Infinity-Stumps/infinity-stumps/simulation/outputs/sim03_trajectory_recovery.png

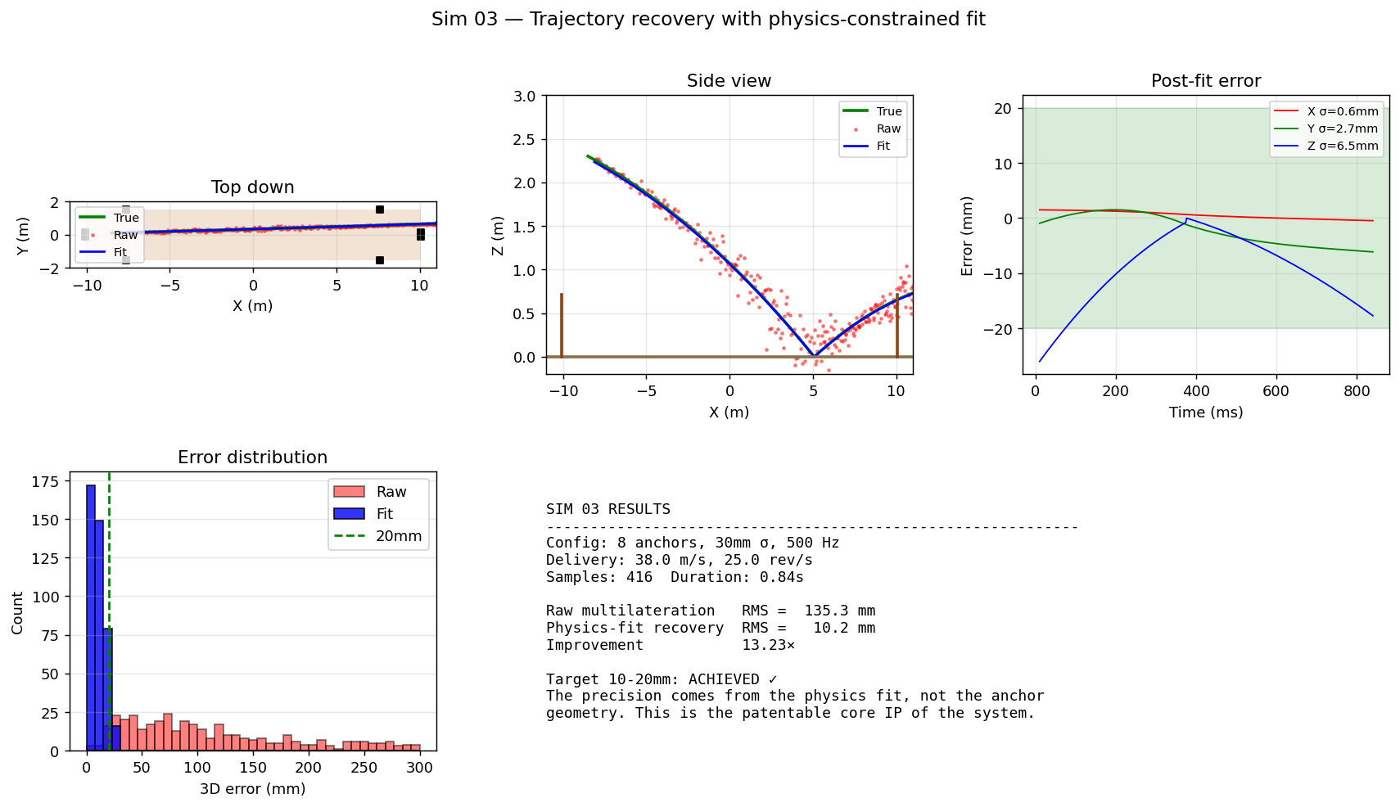
simulation/outputs/sim03_trajectory_recovery.png
