Infinity-Stumps/infinity-stumps/simulation/outputs/sim05_multipath_occlusion.png

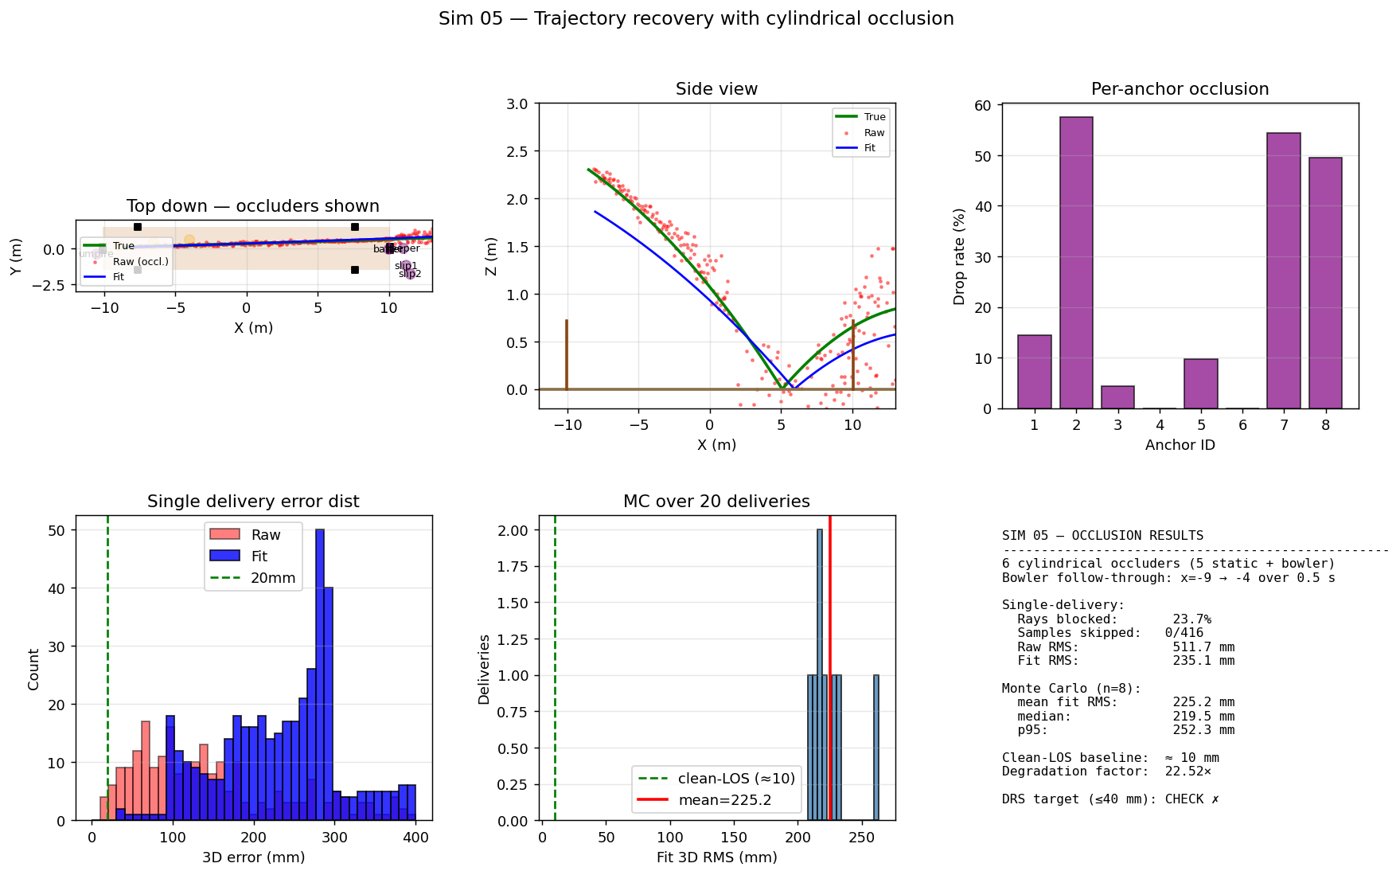
simulation/outputs/sim05_multipath_occlusion.png
