Infinity-Stumps/infinity-stumps/simulation/outputs/sim05b_mitigations.png

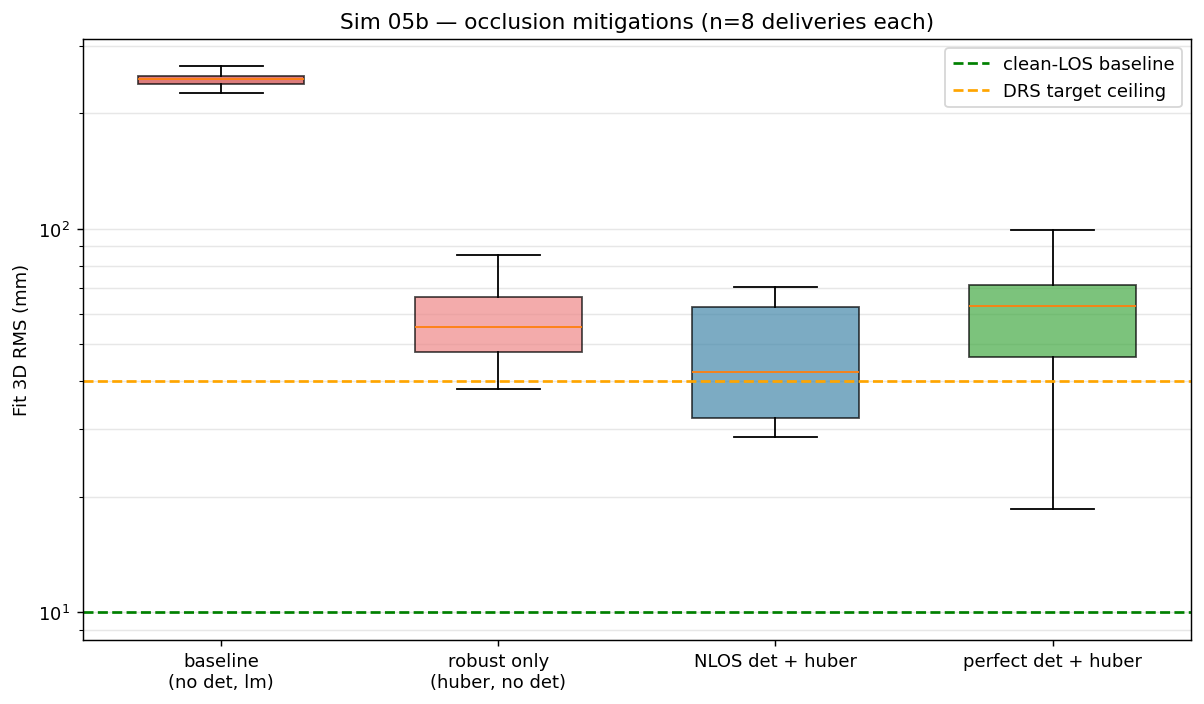
simulation/outputs/sim05b_mitigations.png
