Infinity-Stumps/infinity-stumps/simulation/outputs/sim_ekf.png

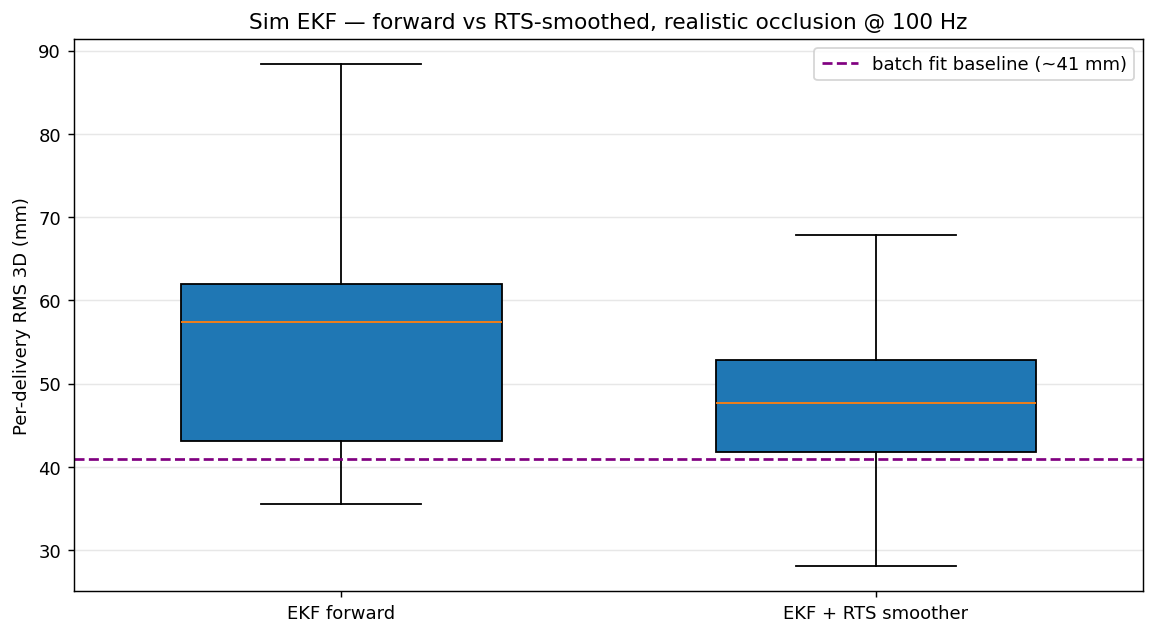
simulation/outputs/sim_ekf.png
