Infinity-Stumps/infinity-stumps/simulation/outputs/sim_lbw.png

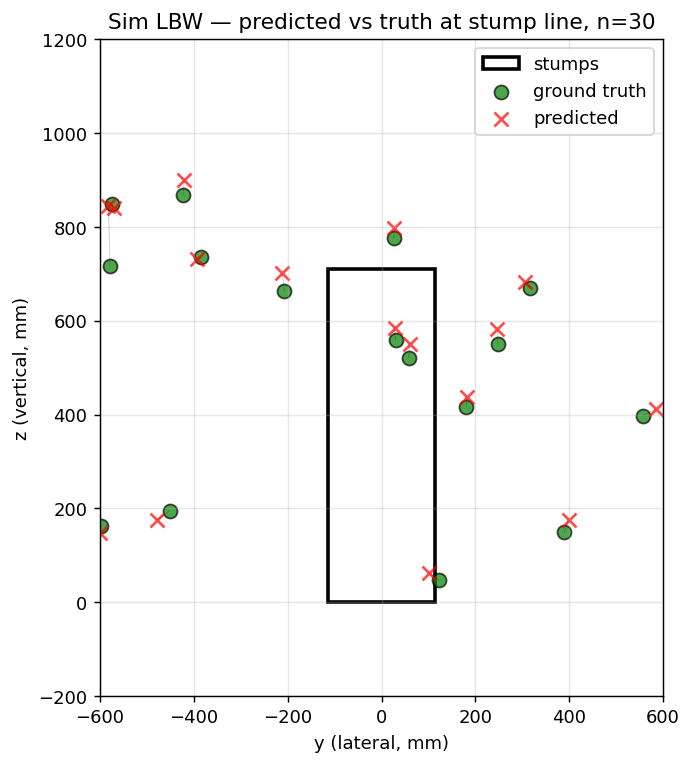
simulation/outputs/sim_lbw.png
