Infinity-Stumps/infinity-stumps/simulation/outputs/sim_ml.png

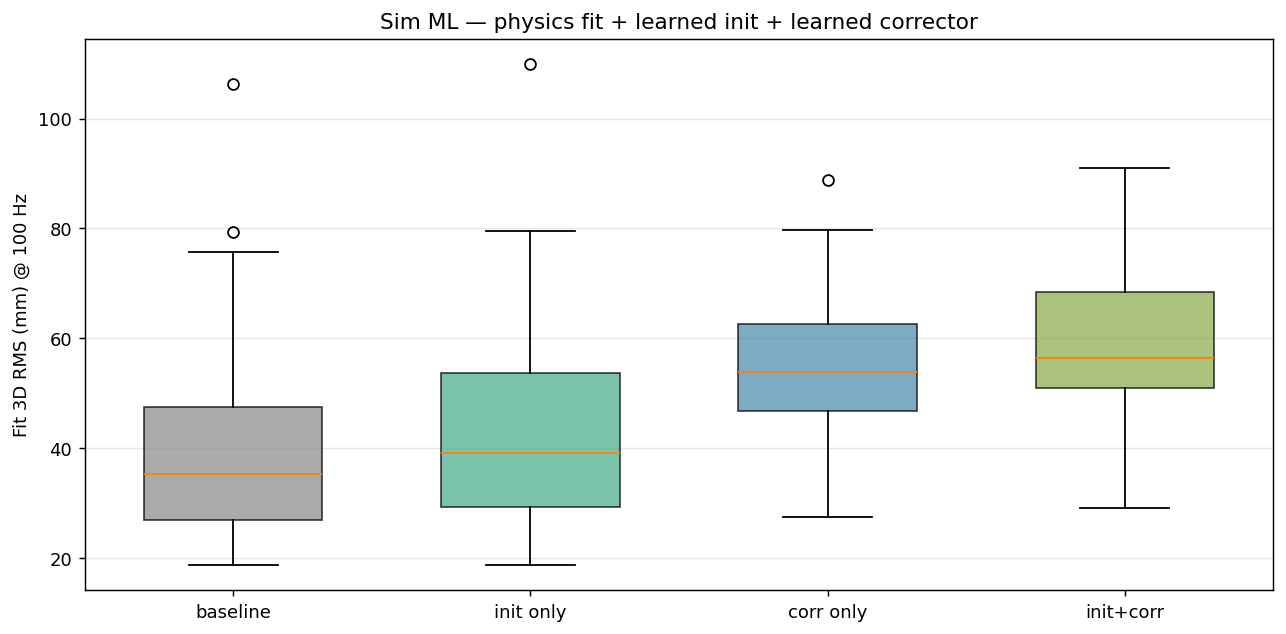
simulation/outputs/sim_ml.png
