Infinity-Stumps/infinity-stumps/simulation/outputs/sim_realistic.png

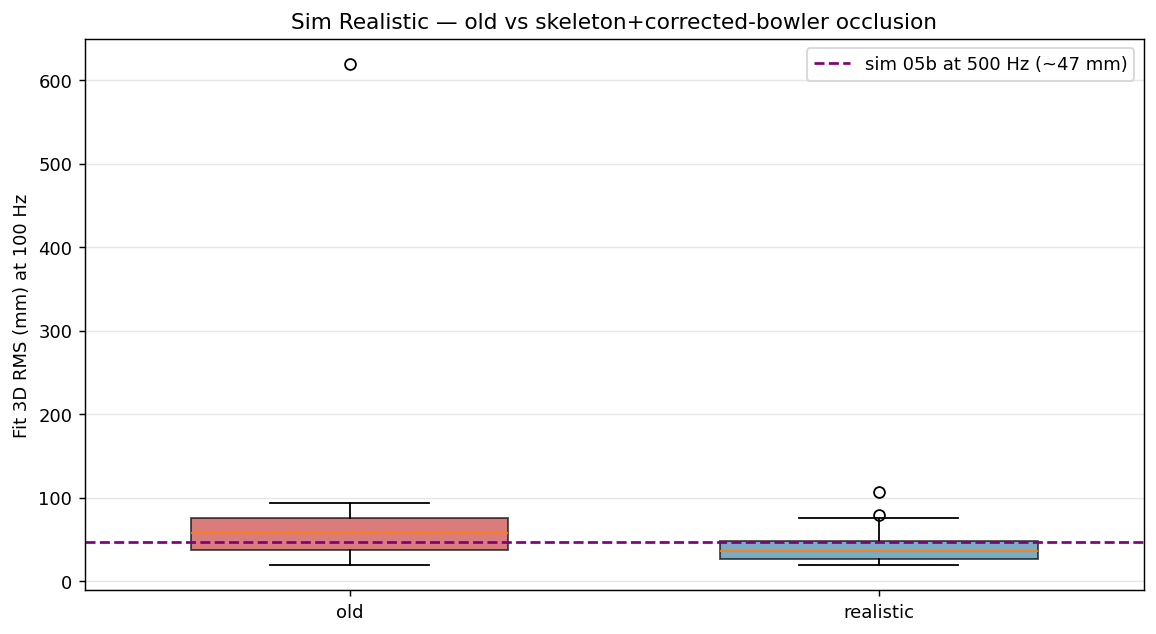
simulation/outputs/sim_realistic.png
