Infinity-Stumps/infinity-stumps/simulation/outputs/upside_sweep.png

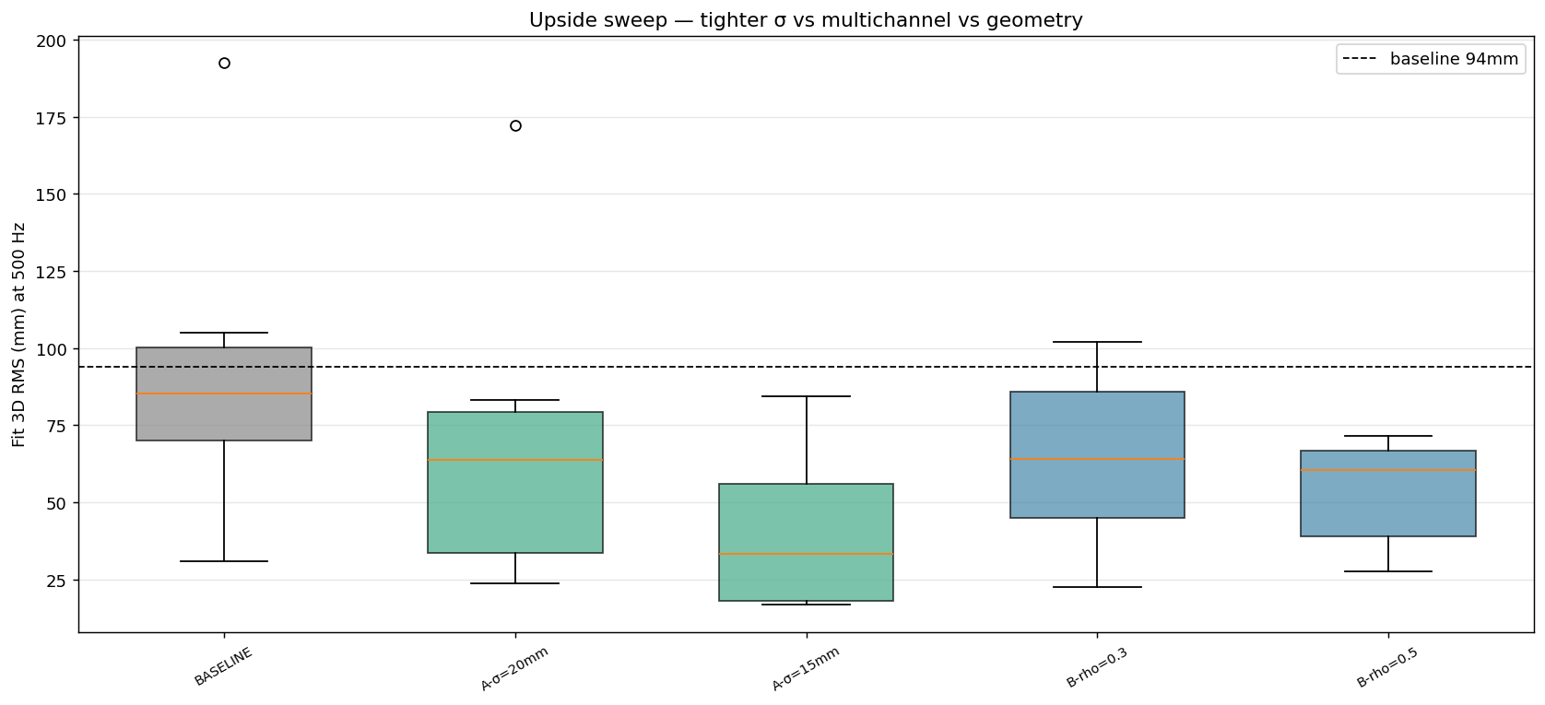
simulation/outputs/upside_sweep.png
