Infinity-Stumps/infinity-stumps/hardware/anchor-board/anchor_board.kicad_sch

## KiCad design hardware/anchor-board/anchor_board.kicad_sch (2026-05-14)

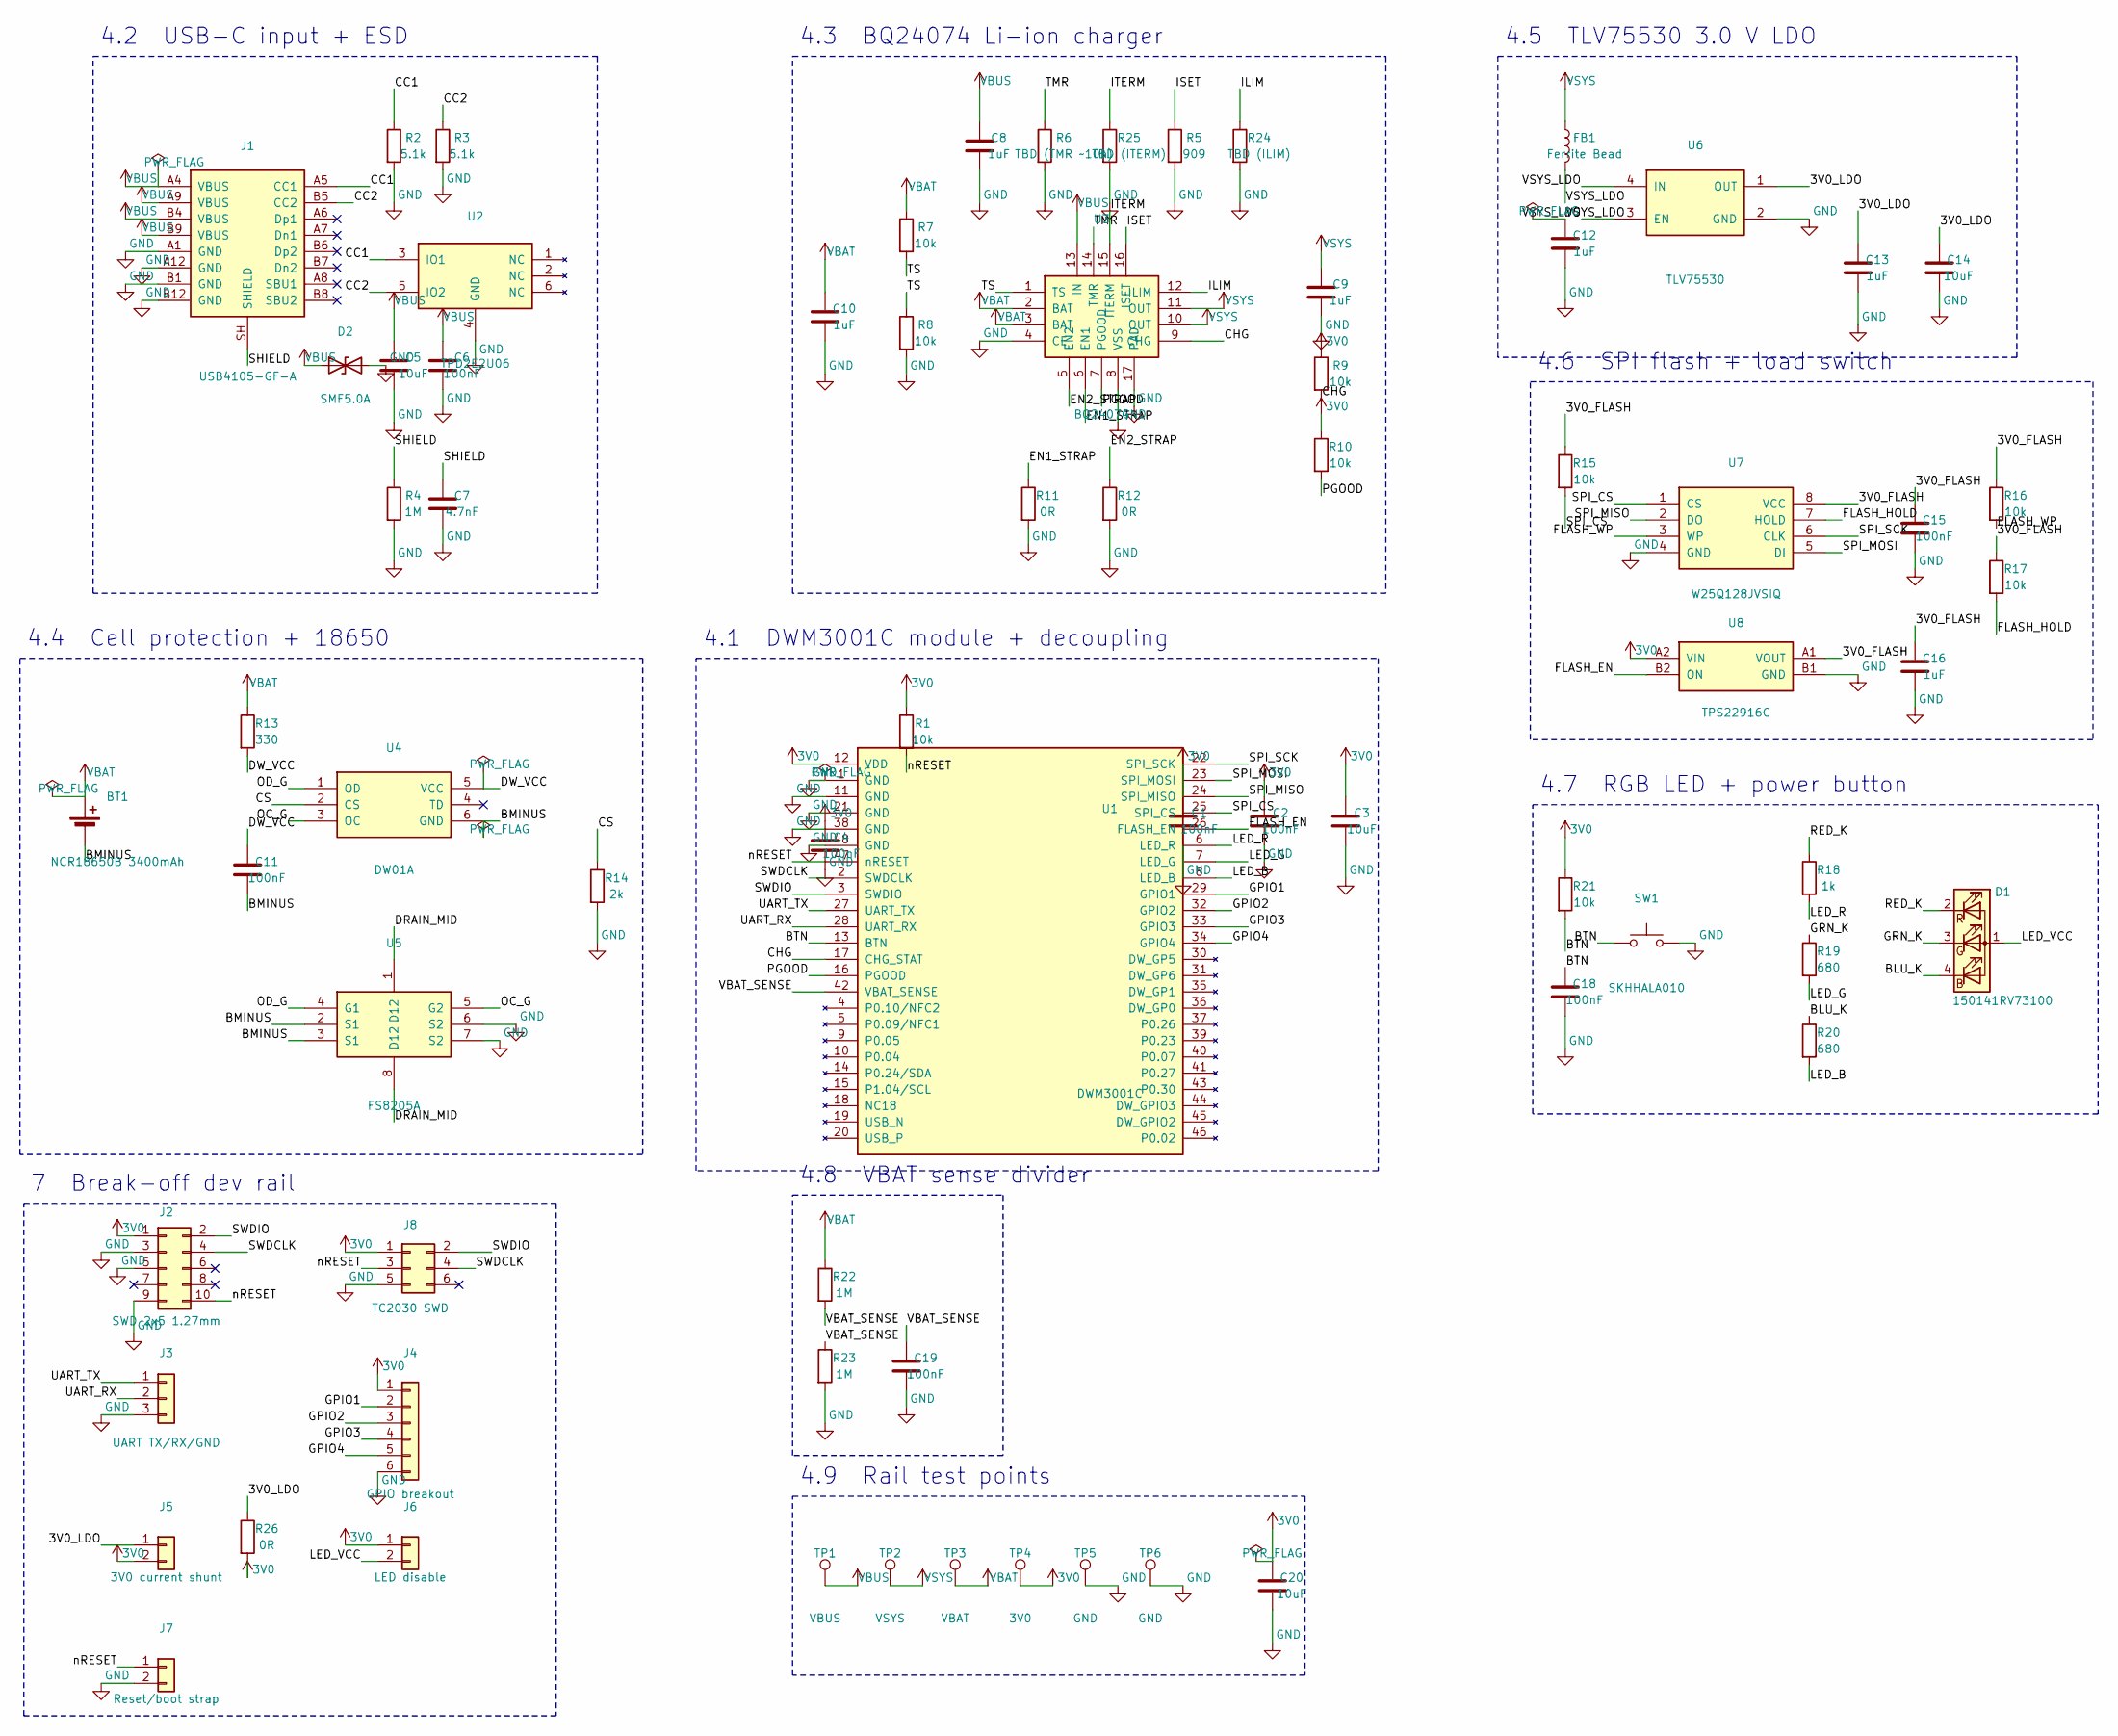
[picture p10: schematic anchor_board.kicad_sch]

Parts:
BT1: NCR18650B 3400mAh; BatteryHolder_Keystone_1042_1x18650
C1, C2, C4, C6, C11, C15, C18, C19: 100nF; C_0402_1005Metric
C3, C5, C14, C20: 10uF; C_0805_2012Metric
C7: 4.7nF; C_0402_1005Metric
C8, C9, C10, C12, C13, C16: 1uF; C_0603_1608Metric
D1: 150141RV73100; LED_RGB_Wuerth-PLCC4_3.2x2.8mm_150141M173100
D2: SMF5.0A; D_SOD-123
FB1: Ferrite Bead; L_0603_1608Metric
J1: USB4105-GF-A; USB_C_Receptacle_GCT_USB4105-xx-A_16P_TopMnt_Horizontal
J2: SWD 2x5 1.27mm; PinHeader_2x05_P1.27mm_Vertical
J3: UART TX/RX/GND; PinHeader_1x03_P2.54mm_Vertical
J4: GPIO breakout; PinHeader_1x06_P2.54mm_Vertical
J5: 3V0 current shunt; PinHeader_1x02_P2.54mm_Vertical
J6: LED disable; PinHeader_1x02_P2.54mm_Vertical
J7: Reset/boot strap; PinHeader_1x02_P2.54mm_Vertical
J8: TC2030 SWD; Tag-Connect_TC2030-IDC-NL_2x03_P1.27mm_Vertical
R1, R7, R8, R9, R10, R15, R16, R17, R21: 10k; R_0402_1005Metric
R2, R3: 5.1k; R_0402_1005Metric
R4, R22, R23: 1M; R_0402_1005Metric
R5: 909; R_0402_1005Metric
R6: TBD (TMR ~10h); R_0402_1005Metric
R11, R12, R26: 0R; R_0402_1005Metric
R13: 330; R_0402_1005Metric
R14: 2k; R_0402_1005Metric
R18: 1k; R_0402_1005Metric
R19, R20: 680; R_0402_1005Metric
R24: TBD (ILIM); R_0402_1005Metric
R25: TBD (ITERM); R_0402_1005Metric
SW1: SKHHALA010; SW_Alps_SKHHAL
TP1: VBUS; TestPoint_Pad_D1.5mm
TP2: VSYS; TestPoint_Pad_D1.5mm
TP3: VBAT; TestPoint_Pad_D1.5mm
TP4: 3V0; TestPoint_Pad_D1.5mm
TP5, TP6: GND; TestPoint_Pad_D1.5mm
U1: DWM3001C
U2: TPD2E2U06; SOT-563
U3: BQ24074; QFN-16-1EP_3x3mm_P0.5mm_EP1.7x1.7mm
U4: DW01A; SOT-23-6
U5: FS8205A; TSSOP-8_4.4x3mm_P0.65mm
U6: TLV75530; X2SON-4_1x1mm_P0.5mm
U7: W25Q128JVSIQ; SOIC-8_3.9x4.9mm_P1.27mm
U8: TPS22916C; WLP-4_0.83x0.83mm_P0.4mm

Connections:
3V0: C1.1, C2.1, C3.1, C4.1, C20.1, J2.1, J4.1, J5.2, J6.1, J8.1, R1.1, R9.1, R10.1, R21.1, R26.2, TP4.1, U1.12 (VDD), U8.A2 (VIN)
3V0_FLASH: C15.1, C16.1, R15.1, R16.1, R17.1, U7.8 (VCC), U8.A1 (VOUT)
3V0_LDO: C13.1, C14.1, J5.1, R26.1, U6.1 (OUT)
BLU_K: D1.4 (BK), R20.1
BMINUS: BT1.2 (-), C11.2, U4.6 (GND), U5.2 (S1), U5.3 (S1)
BTN: C18.1, R21.2, SW1.1, U1.13 (BTN)
CC1: J1.A5 (CC1), R2.1, U2.3 (IO1)
CC2: J1.B5 (CC2), R3.1, U2.5 (IO2)
CHG: R9.2, U1.17 (CHG_STAT), U3.9 (CHG)
CS: R14.1, U4.2 (CS)
DRAIN_MID: U5.1 (D12), U5.8 (D12)
DW_VCC: C11.1, R13.2, U4.5 (VCC)
EN1_STRAP: R11.1, U3.6 (EN1)
EN2_STRAP: R12.1, U3.5 (EN2)
FLASH_EN: U1.26 (FLASH_EN), U8.B2 (ON)
FLASH_HOLD: R17.2, U7.7 (HOLD)
FLASH_WP: R16.2, U7.3 (WP)
GND: C1.2, C2.2, C3.2, C4.2, C5.2, C6.2, C7.2, C8.2, C9.2, C10.2, C12.2, C13.2, C14.2, C15.2, C16.2, C18.2, C19.2, C20.2, D2.2 (A2), J1.A1 (GND), J1.A12 (GND), J1.B1 (GND), J1.B12 (GND), J2.3, J2.5, J2.9, J3.3, J4.6, J7.2, J8.5, R2.2, R3.2, R4.2, R5.2, R6.2, R8.2, R11.2, R12.2, R14.2, R23.2, R24.2, R25.2, SW1.2, TP5.1, TP6.1, U1.1 (GND), U1.11 (GND), U1.21 (GND), U1.38 (GND), U1.48 (GND), U2.4 (GND), U3.4 (CE), U3.8 (VSS), U3.17 (PAD), U5.6 (S2), U5.7 (S2), U6.2 (GND), U7.4 (GND), U8.B1 (GND)
GPIO1: J4.2, U1.29 (GPIO1)
GPIO2: J4.3, U1.32 (GPIO2)
GPIO3: J4.4, U1.33 (GPIO3)
GPIO4: J4.5, U1.34 (GPIO4)
GRN_K: D1.3 (GK), R19.1
ILIM: R24.1, U3.12 (ILIM)
ISET: R5.1, U3.16 (ISET)
ITERM: R25.1, U3.15 (ITERM)
LED_B: R20.2, U1.8 (LED_B)
LED_G: R19.2, U1.7 (LED_G)
LED_R: R18.2, U1.6 (LED_R)
LED_VCC: D1.1 (A), J6.2
OC_G: U4.3 (OC), U5.5 (G2)
OD_G: U4.1 (OD), U5.4 (G1)
PGOOD: R10.2, U1.16 (PGOOD), U3.7 (PGOOD)
RED_K: D1.2 (RK), R18.1
SHIELD: C7.1, J1.SH (SHIELD), R4.1
SPI_CS: R15.2, U1.25 (SPI_CS), U7.1 (CS)
SPI_MISO: U1.24 (SPI_MISO), U7.2 (DO)
SPI_MOSI: U1.23 (SPI_MOSI), U7.5 (DI)
SPI_SCK: U1.22 (SPI_SCK), U7.6 (CLK)
SWDCLK: J2.4, J8.4, U1.2 (SWDCLK)
SWDIO: J2.2, J8.2, U1.3 (SWDIO)
TMR: R6.1, U3.14 (TMR)
TS: R7.2, R8.1, U3.1 (TS)
UART_RX: J3.2, U1.28 (UART_RX)
UART_TX: J3.1, U1.27 (UART_TX)
VBAT: BT1.1 (+), C10.1, R7.1, R13.1, R22.1, TP3.1, U3.2 (BAT), U3.3 (BAT)
VBAT_SENSE: C19.1, R22.2, R23.1, U1.42 (VBAT_SENSE)
VBUS: C5.1, C6.1, C8.1, D2.1 (A1), J1.A4 (VBUS), J1.A9 (VBUS), J1.B4 (VBUS), J1.B9 (VBUS), TP1.1, U3.13 (IN)
VSYS: C9.1, FB1.1, TP2.1, U3.10 (OUT), U3.11 (OUT)
VSYS_LDO: C12.1, FB1.2, U6.3 (EN), U6.4 (IN)
nRESET: J2.10, J7.1, J8.3, R1.2, U1.47 (nRESET)

Notes on the sheet:
4.1 DWM3001C module + decoupling
4.2 USB-C input + ESD
4.3 BQ24074 Li-ion charger
4.4 Cell protection + 18650
4.5 TLV75530 3.0 V LDO
4.6 SPI flash + load switch
4.7 RGB LED + power button
4.8 VBAT sense divider
4.9 Rail test points
7 Break-off dev rail
